lzrtag/LZRTag/ESP/ServerConfig.lua

game = {
	brightness 	= 0,
	team			= 7,
}

player = {
	dead = false,
	ammo = 3,
	shotCooldown = false,
	marked = false
}

hitConfDefaults = {
	hitFlashBrightness 	= 4,
	hitFlashDuration   	= 100,
	hitVibration			= 100,

	deathFlashBrightness = 10,
	deathFlashDuration	= 1500,
	deathBrightness		= 1,
	deathVibration			= 1500,
}
hitConf = hitConfDefaults;

fireConfDefaults = {
	ammoCap 			= 18,
	perReloadAmmo 	= 4,

	reloadDelay = 2000,

	salveNum = 2,
	perShotDelay	= 150,

	flashBrightness = 10,

	shotLocked = true,
	reportButton = false,
}
fireConf = fireConfDefaults;

function update_vest_brightness()
	if(player.dead) then
		setVestBrightness(hitConf.deathBrightness);
	elseif(player.marked) then
		setVestBrightness(5);
	else
		setVestBrightness(game.brightness);
	end
end

-- luacheck: globals updateAmmo attemptShot
subscribeTo(playerTopic .. "/Ammo/Set", 1,
	function(data)
		data = tonumber(data);
		if(data) then
			updateAmmo(data);
			attemptShot();
		end
	end);

subscribeTo(playerTopic .. "/ID", 1,
	function(data)
		player.id = tonumber(data);
		if(player.id) then
			uart.write(0, 100, player.id);
		end
	end);

subscribeTo(playerTopic .. "/Team", 1,
	function(data)
		game.team = tonumber(data) or 7;
		setVestColor(game.team);
	end);
subscribeTo(playerTopic .. "/FX/Brightness", 1,
	function(data)
		game.brightness = tonumber(data) or 0;

		if((game.brightness == 2) or (game.brightness == 3)) then
			game.brightness = game.brightness + 4;
		end

		update_vest_brightness();
	end);

subscribeTo(playerTopic .. "/FX/Heartbeat", 1,
	function(data)
		setVibratePattern(tonumber(data) or 0);
	end
);
subscribeTo(playerTopic .. "/FX/Marked", 1,
	function(data)
		player.marked = (data == "1");
		update_vest_brightness();
	end);

hitConfOptions = {
	metatable = {
		__index = hitConfDefaults}};
subscribeTo(playerTopic .. "/HitConf", 1,
	function(data)
		if(data == nil or data:len() < 2) then
			hitConf = hitConfDefaults
		else
			hitConf = sjson.decode(data, hitConfOptions);
		end
	end);

fireConfOptions = {
	metatable = {
		__index = fireConfDefaults}}
subscribeTo(playerTopic .. "/FireConf", 1,
	function(data)
		if(data == nil or data:len() < 2) then
			fireConf = fireConfDefaults
		else
			fireConf = sjson.decode(data, fireConfOptions);
		end
	end);
