lzrtag/LZRTag/ESP/init.lua

dofile("PlayerData.lc");
playerTopic = lasertagTopic .. "/Players/"..playerID;

dofile("MQTTConnect.lc");

StartSymbol = string.byte("!");

SAFEMODE = file.exists("BOOT_SAFECHECK");
systemIsSetUp = false;

tmr.create():alarm(2000, tmr.ALARM_SINGLE,
	function(t)

		uart.setup(0, 31250, 8, uart.PARITY_NONE, uart.STOPBITS_1, 0);

		noTagTimer = tmr.create();
		noTagTimer:alarm(1000, tmr.ALARM_SINGLE,
			function(tt)
				uart.on("data");
				uart.setup(0, 115200, 8, uart.PARITY_NONE, uart.STOPBITS_1, 1);

				print("\nNo Lasertag attached, returning to normal mode!\n");
			end
		);

		uart.on("data", 0,
			function(data)
				data = string.byte(data);
				if(data == StartSymbol) then
					noTagTimer:unregister();

					uart.write( 0, 10, 100, 0,					-- Vibrate a little
									11, 100, 0, 164, 1, 164, 1,-- Connect buzz
									101, 4);							-- Set blue team

					uart.on("data", 0, function(d) end, 0);

					onMQTTConnect(
						function()
							dofile("ConsoleRedir.lc");

							if(not(SAFEMODE)) then
								file.open("BOOT_SAFECHECK","w"):close();

								dofile("MQTTPing.lc");
								dofile("Lasertag.lc");
								dofile("ServerConfig.lc")
								dofile("FireHandling.lc");

								tmr.create():alarm(1500, tmr.ALARM_SINGLE,
									function()
										file.remove("BOOT_SAFECHECK");
									end);
							else
								uart.write(	0, 200, 10,	-- Bright blink mode
												101, 1,		-- Red team
												11, 235, 3, 0x80, 0x7, 0xF8, 0x7); -- 2kHz "error" buzz
								homeQTT:publish(playerTopic .. "/Connection", "SAFEMODE", 0, 1);
							end
						end
					);
				end
			end
		, 0);

		-- Flush any potential buffer, then send the start signal
		uart.write(0, 255, 255, 255, 255, 255, 255, StartSymbol);
	end
);
