lzrtag/LZRTag/ESP32/Main/main/core/IR.h

/*
 * IR.h
 *
 *  Created on: 18 Feb 2019
 *      Author: xasin
 */

#ifndef MAIN_CORE_IR_H_
#define MAIN_CORE_IR_H_

#include "setup.h"

namespace LZR {
namespace IR {

void init();
void send_signal(int8_t cCode = -1);

}
}


#endif /* MAIN_CORE_IR_H_ */
