lzrtag/LZRTag/ESP32/Main/main/fx/colorSets.h

/*
 * colorSets.h
 *
 *  Created on: 15 Mar 2019
 *      Author: xasin
 */

#ifndef MAIN_FX_COLORSETS_H_
#define MAIN_FX_COLORSETS_H_

#include "animatorThread.h"

namespace LZR {

extern const ColorSet 	teamColors[];
extern const FXSet		brightnessLevels[];

}
#endif /* MAIN_FX_COLORSETS_H_ */
