lzrtag/LZRTag/ESP32/Main/main/fx/sounds.h

/*
 * sounds.h
 *
 *  Created on: 30 Mar 2019
 *      Author: xasin
 */

#ifndef MAIN_FX_SOUNDS_H_
#define MAIN_FX_SOUNDS_H_

#include <string>

namespace LZR {
namespace Sounds {

void play_audio(std::string aName);
void init();

}
}

#endif /* MAIN_FX_SOUNDS_H_ */
