lzrtag/LZRTag/ESP32/Main/main/test.h

#include <stdint.h>
#include <xasin/audio.h>

const Xasin::Audio::opus_audio_bundle_t encoded_audio_test = {
	40, 361, 255, (const uint8_t[]){

		120, 0, 177, 45, 168, 133, 222, 145, 39,
		190, 253, 177, 2, 51, 48, 200, 131, 22,
		183, 18, 119, 197, 77, 12, 48, 248, 121,
		167, 171, 186, 105, 96, 172, 108, 243, 246,
		185, 187, 182, 231, 120, 21, 126, 219, 68,
		118, 57, 144, 187, 121, 158, 210, 227, 227,
		17, 39, 80, 113, 6, 166, 243, 14, 230,
		239, 219, 0, 165, 146, 92, 188, 20, 96,
		141, 121, 198, 222, 219, 64, 235, 21, 120,
		21, 35, 184, 239, 117, 228, 157, 70, 25,
		221, 194, 130, 120, 242, 220, 105, 161, 39,
		117, 202, 108, 225, 252, 33, 46, 126, 103,
		224, 125, 70, 85, 200, 164, 124, 122, 207,
		129, 94, 244, 104, 18, 89, 220, 27, 123,
		237, 97, 240, 129, 71, 121, 9, 63, 107,
		71, 210, 214, 44, 17, 224, 3, 226, 78,
		199, 39, 89, 142, 163, 95, 72, 25, 75,
		56, 255, 64, 110, 93, 65, 196, 104, 21,
		30, 146, 47, 159, 255, 121, 193, 14, 247,
		93, 97, 158, 0, 73, 206, 72, 12, 129,
		73, 187, 152, 20, 158, 131, 22, 102, 31,
		239, 6, 110, 210, 211, 45, 21, 161, 233,
		240, 139, 104, 17, 254, 184, 237, 133, 168,
		10, 80, 83, 6, 244, 3, 186, 150, 215,
		155, 119, 11, 57, 98, 154, 249, 135, 129,
		199, 99, 20, 242, 130, 24, 66, 68, 101,
		152, 0, 170, 96, 54, 239, 104, 18, 189,
		76, 44, 91, 37, 207, 36, 243, 49, 124,
		176, 18, 20, 98, 154, 89, 146, 187, 214,
		82, 151, 85, 165, 252, 71, 130, 106, 225,
		33, 178, 122, 212, 244, 40, 212, 92, 68,
		163, 104, 21, 126, 207, 3, 151, 93, 15,
		252, 64, 2, 145, 37, 66, 231, 111, 39,
		102, 241, 17, 101, 96, 178, 44, 32, 64,
		111, 104, 172, 3, 162, 48, 158, 174, 33,
		82, 225, 8, 161, 103, 104, 134, 213, 66,
		136, 148, 128, 45, 225, 18, 91, 50, 156,
		194, 252, 31, 210, 124, 223, 70, 100, 42,
		170, 16, 94, 160, 124, 52, 176, 209, 89,
		127, 198, 98, 24, 43, 22, 140, 93, 185,
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
}};
